hamster/defcon30/jack/images/IMG_3410.JPG

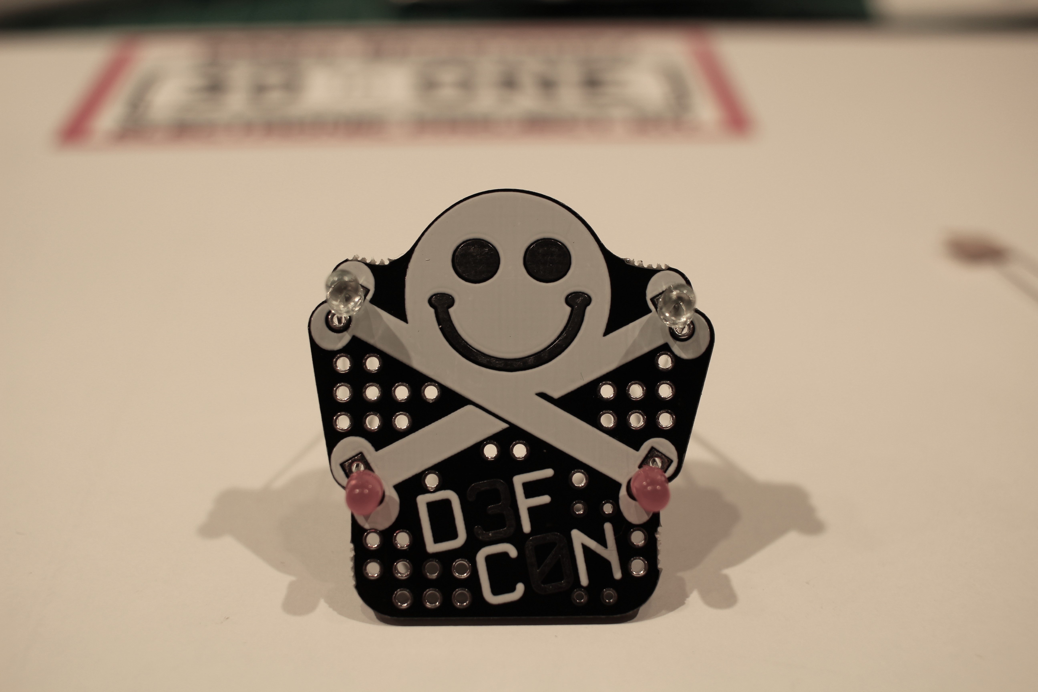
jack/images/IMG_3410.JPG
