hamster/defcon30/jack/images/IMG_3413.JPG

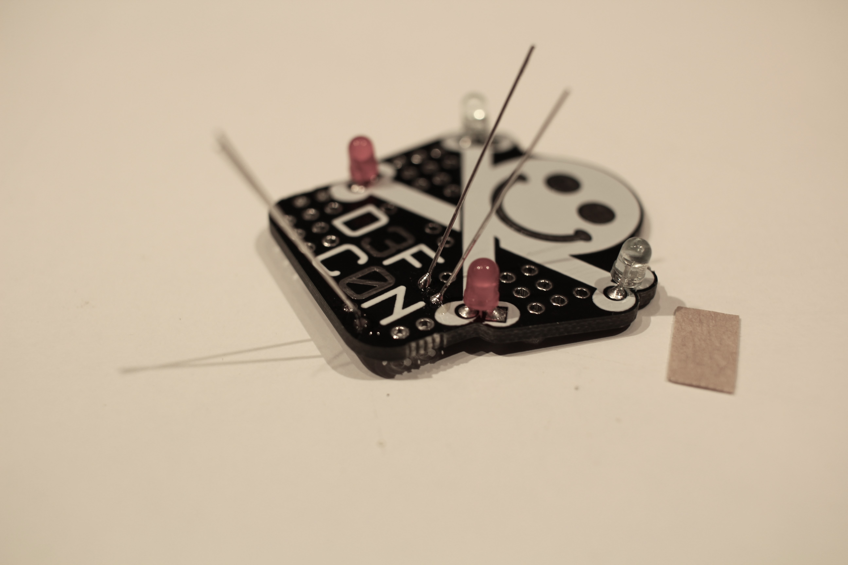
jack/images/IMG_3413.JPG
