hamster/defcon30/jack/images/jack_Eco.png

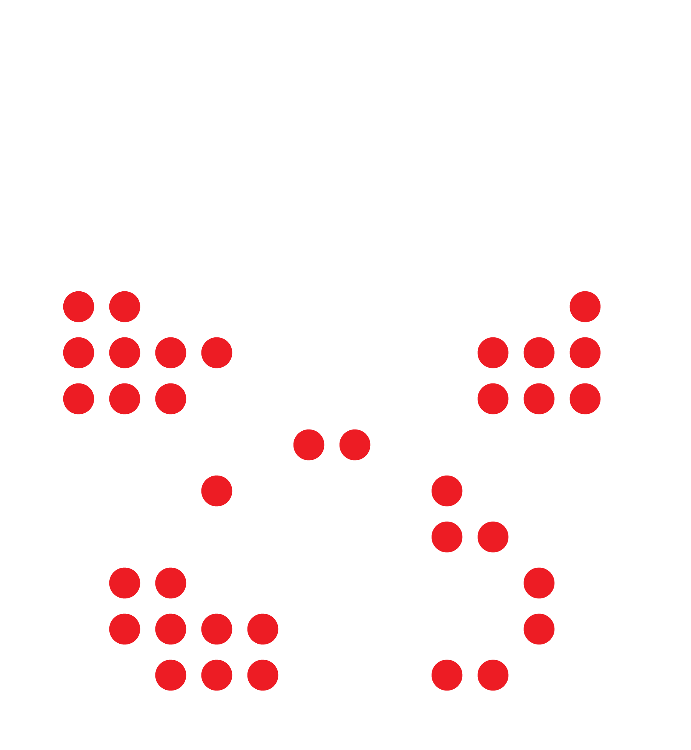
jack/images/jack_Eco.png
