hamster/defcon30/jack/images/jack_Front.png

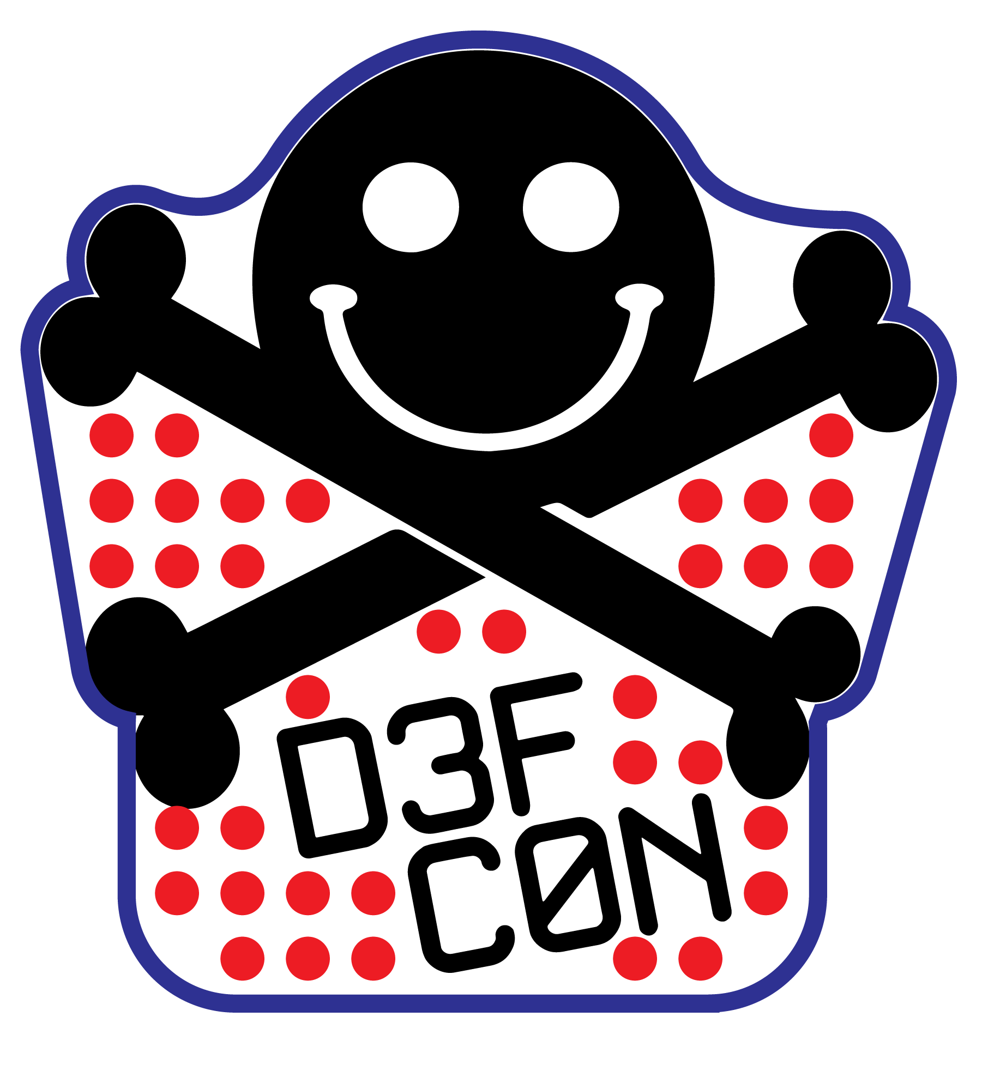
jack/images/jack_Front.png
