hamster/defcon30/jack/images/jack_Mask.png

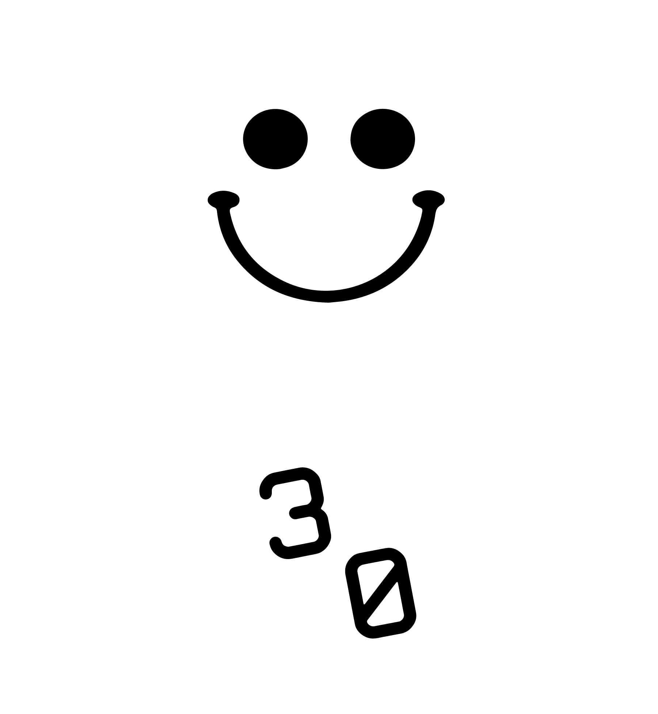
jack/images/jack_Mask.png
