hamster/defcon30/jack/images/jack_Silkscreen.png

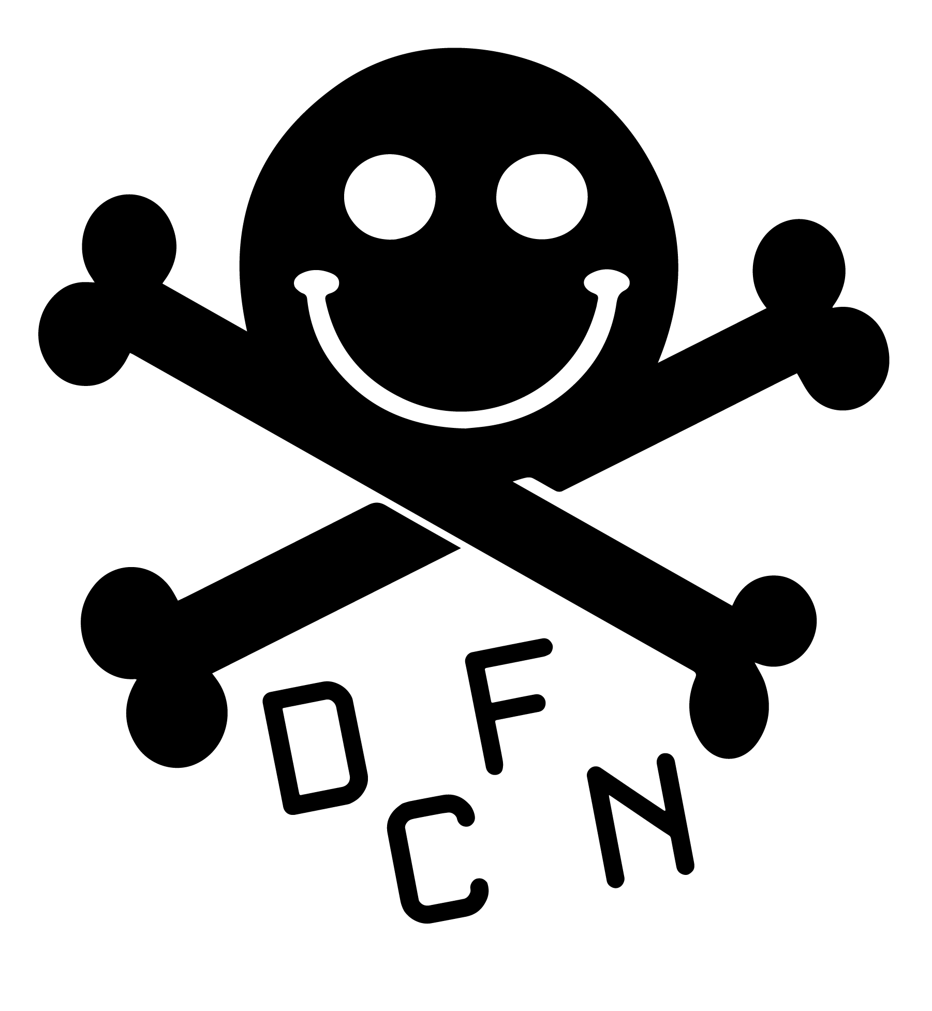
jack/images/jack_Silkscreen.png
