hamster/defcon30/modem/images/modem_Outline.png

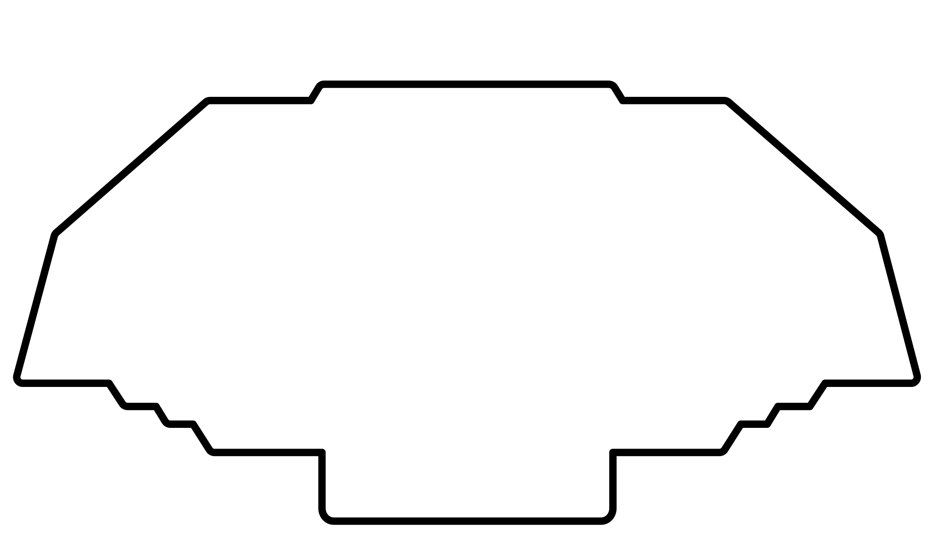
modem/images/modem_Outline.png
