hamster/defcon30/modem/images/modem_Silkscreen.png

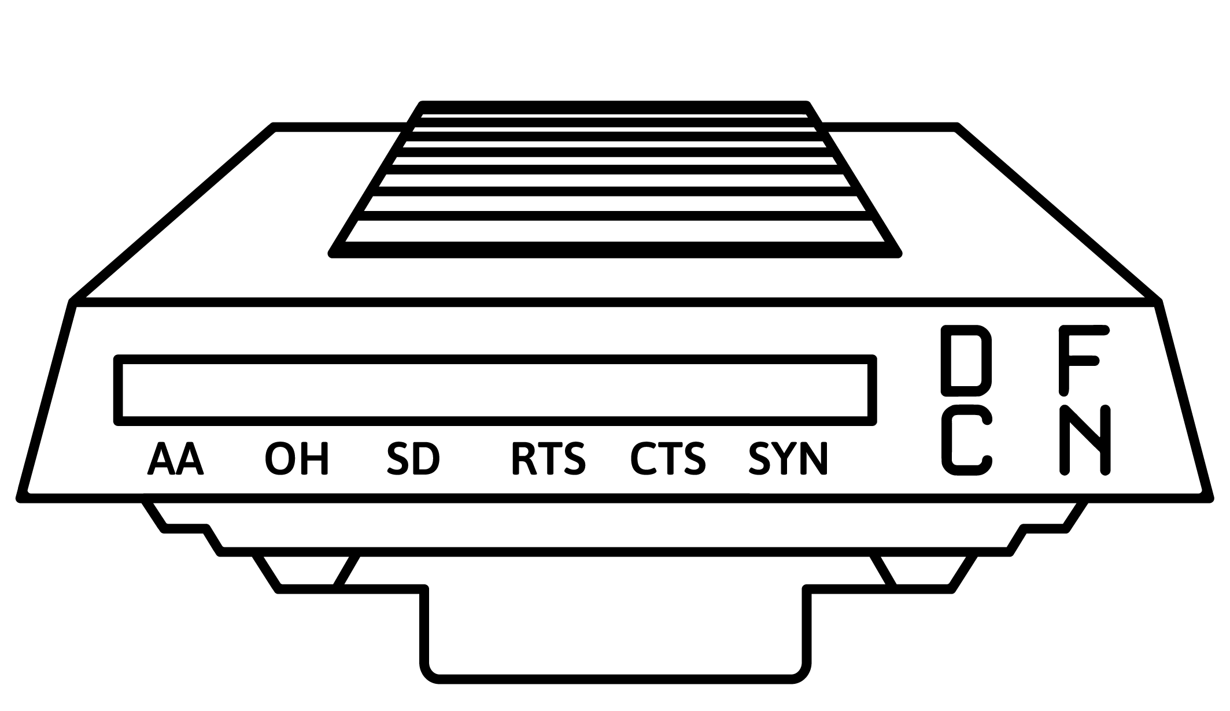
modem/images/modem_Silkscreen.png
